modo-co/modotabmount/images/modotabmount_animat.gif

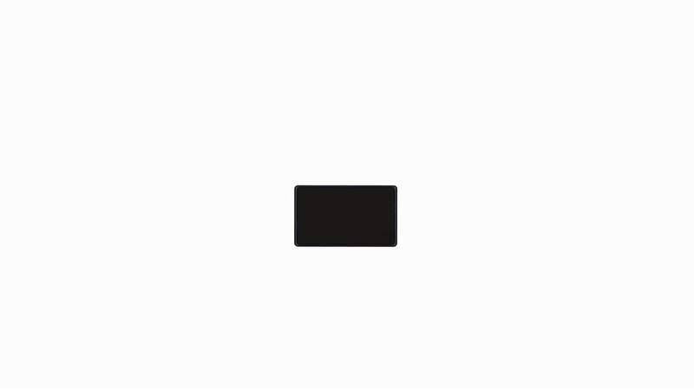
images/modotabmount_animat.gif
