modo-co/modotabmount/images/mtm_basic_back.png

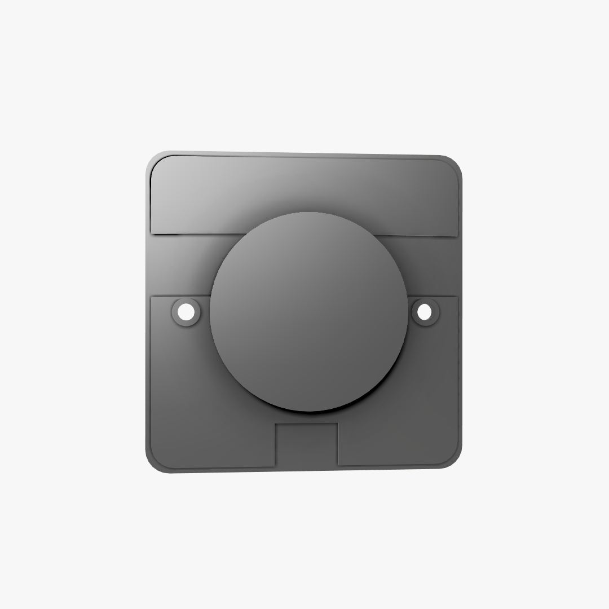
images/mtm_basic_back.png
