modo-co/modotabmount/images/mtm_basic_dimmensions.png

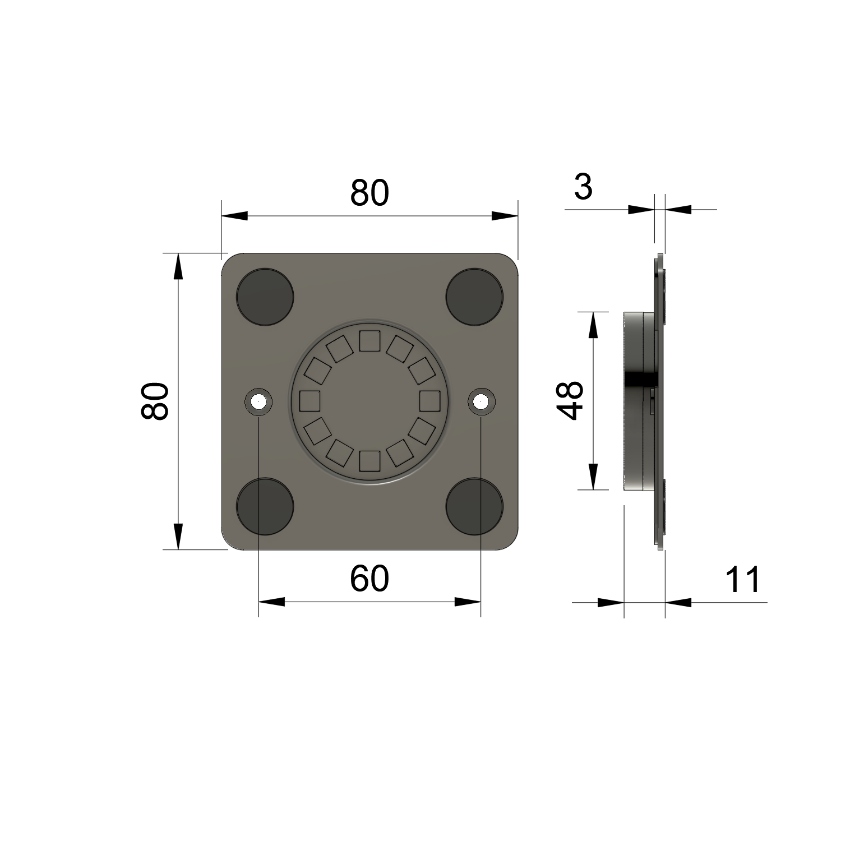
images/mtm_basic_dimmensions.png
