modo-co/modotabmount/images/mtm_smart_2.png

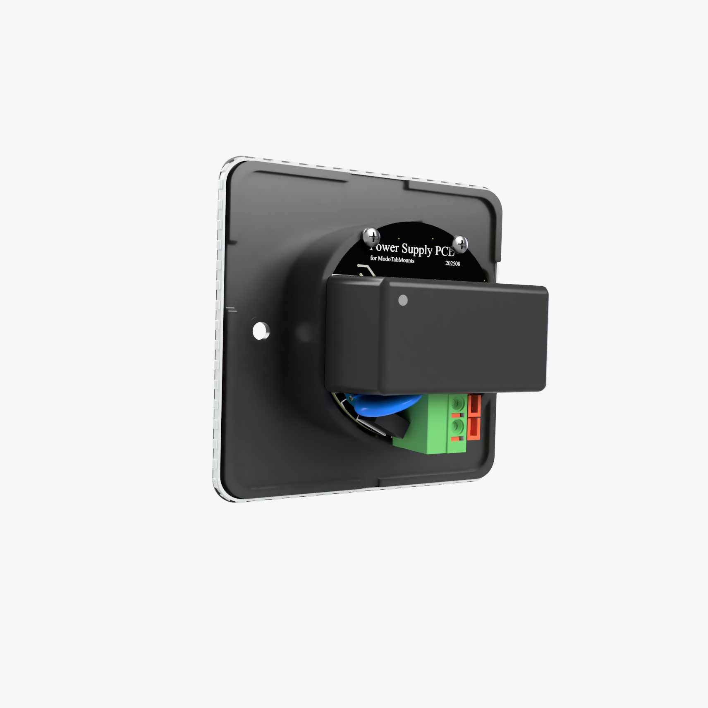
images/mtm_smart_2.png
