modo-co/modotabmount/images/mtm_smart_3.png

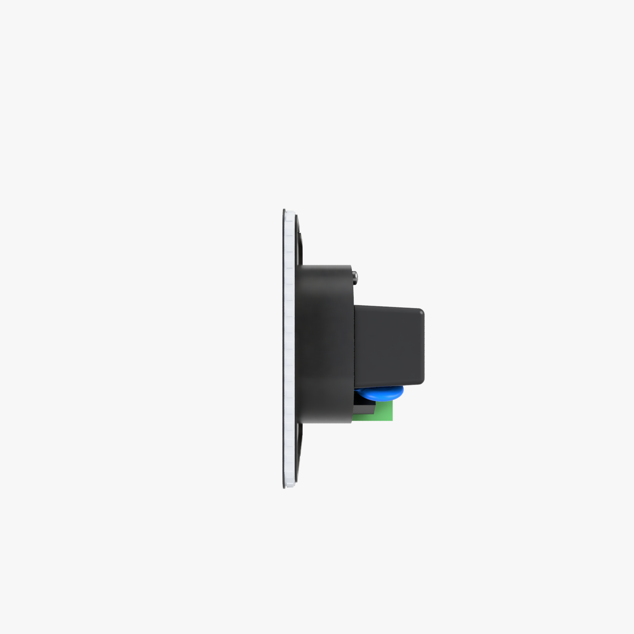
images/mtm_smart_3.png
