modo-co/modotabmount/images/mtm_smart_4.png

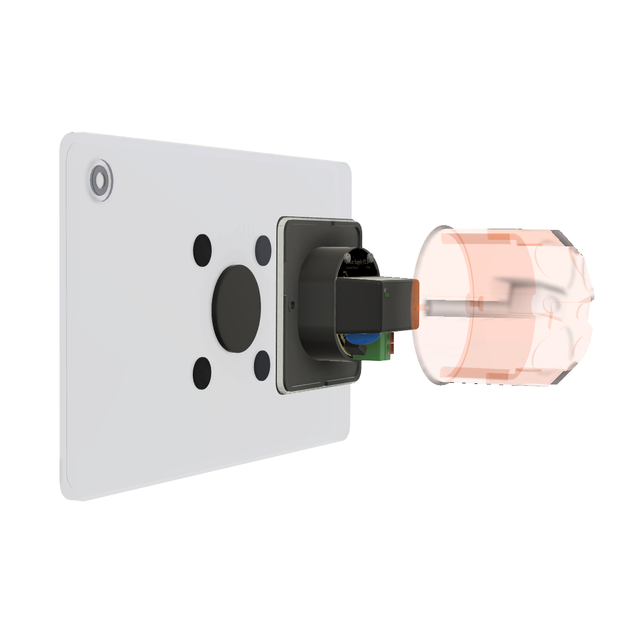
images/mtm_smart_4.png
