modo-co/modotabmount/images/psu_bottom.png

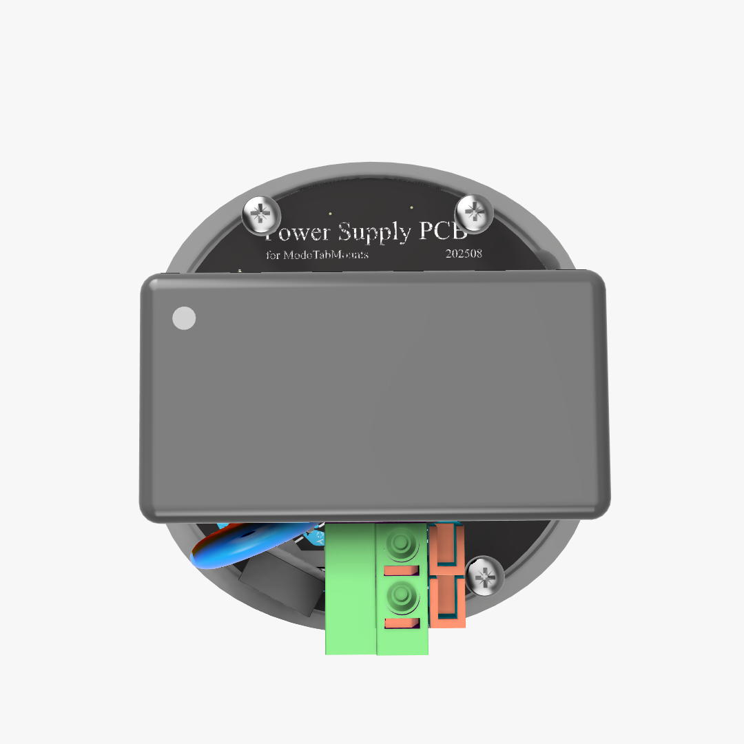
images/psu_bottom.png
