modo-co/modotabmount/images/psu_side.png

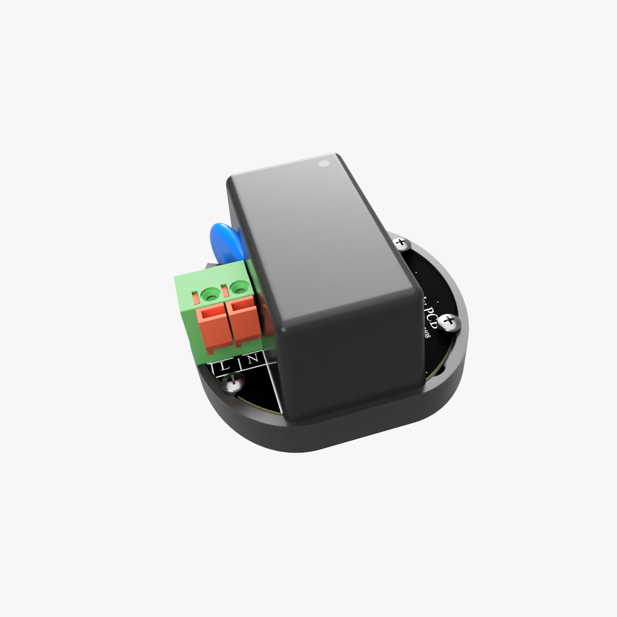
images/psu_side.png
