modo-co/modotabmount/PCB/pcb_bottom.png

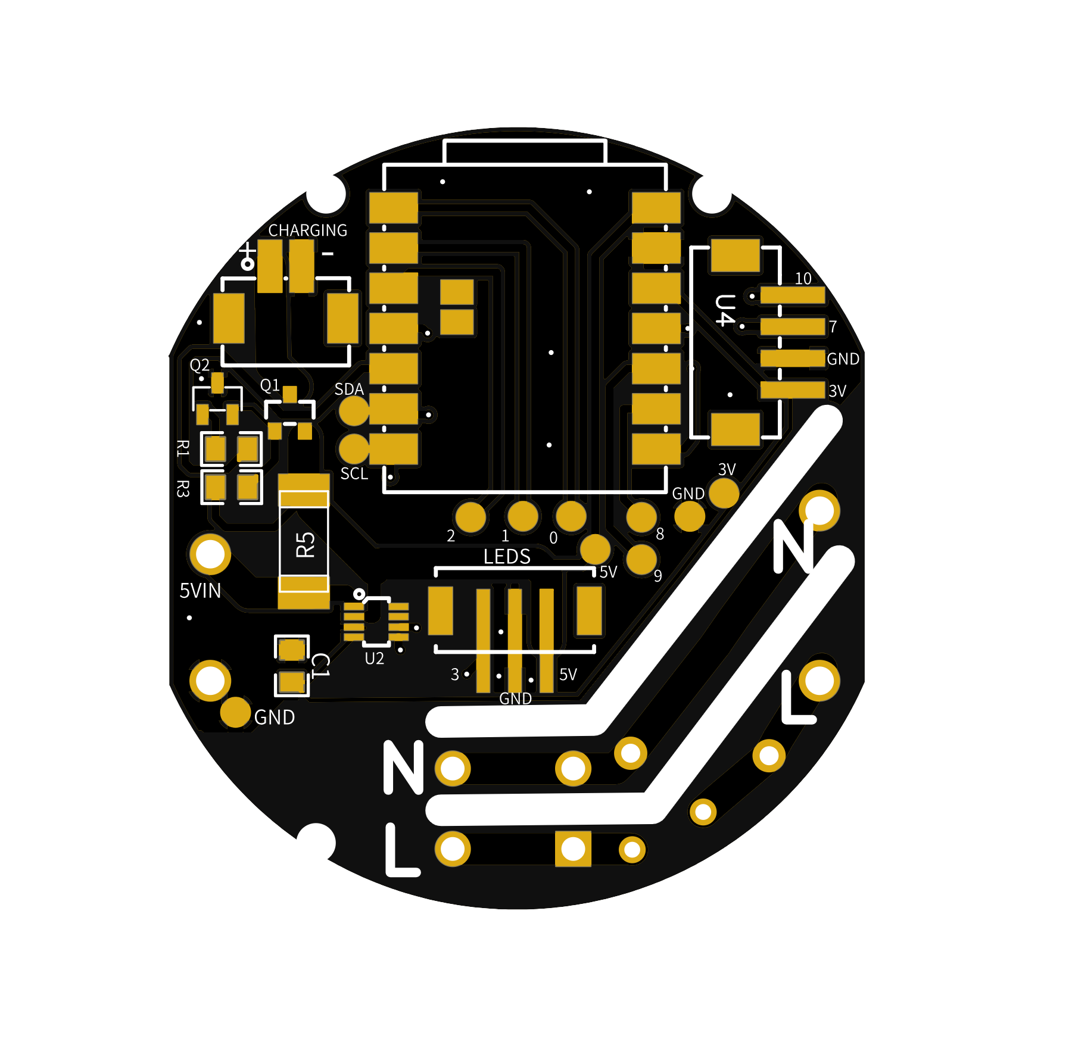
PCB/pcb_bottom.png
