modo-co/modotabmount/PCB/pcb_top.png

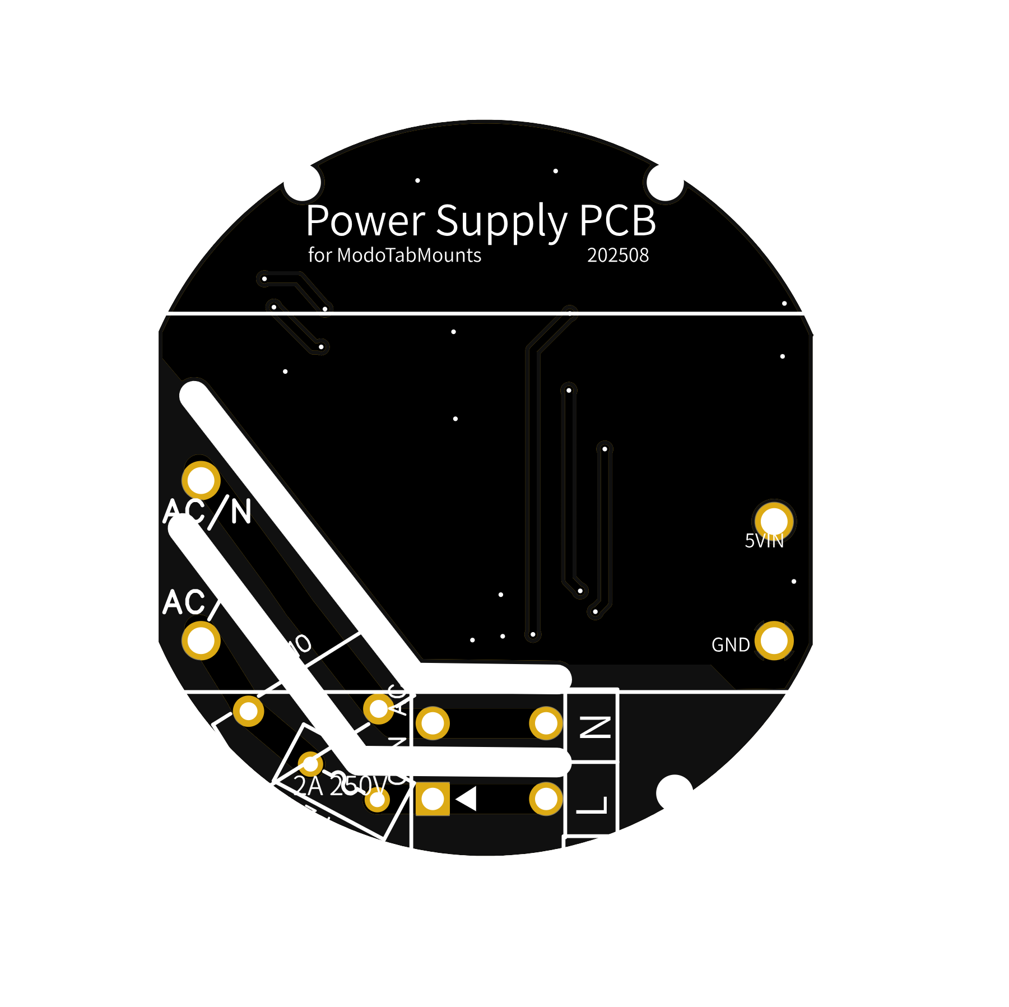
PCB/pcb_top.png
